sanjayaherath/Child-Watch/sketches/time_ds3231/time_ds3231.ino

// Date and time functions using a DS3231 RTC connected via I2C and Wire lib
#include <Wire.h>
#include "RTClib.h"

RTC_DS3231 rtc;

//char daysOfTheWeek[7][12] = {"Sunday", "Monday", "Tuesday", "Wednesday", "Thursday", "Friday", "Saturday"};

void setup () {


  Serial.begin(9600);

  delay(3000); // wait for console opening

  if (! rtc.begin()) {
    Serial.println("Couldn't find RTC");
    while (1);
  }

  if (rtc.lostPower()) {
    
    rtc.adjust(DateTime(F(__DATE__), F(__TIME__)));
    // This line sets the RTC with an explicit date & time, for example to set
    // January 1, 2000 at 12am you would call:
     rtc.adjust(DateTime(2000, 1, 1, 0, 0, 0));
  }
}

void loop () {
    DateTime now = rtc.now();
    
    Serial.print(now.year(), DEC);
    Serial.print('/');
    Serial.print(now.month(), DEC);
    Serial.print('/');
    Serial.print(now.day(), DEC);
    Serial.print(" ");
    //Serial.print(daysOfTheWeek[now.dayOfTheWeek()]);
    //Serial.print(") ");
    Serial.print(now.hour(), DEC);
    Serial.print(':');
    Serial.print(now.minute(), DEC);
    Serial.print(':');
    Serial.print(now.second(), DEC);
    Serial.println();
    
    
    
    
    delay(3000);
}
