sanjayaherath/Child-Watch/sketches/FONAtest2/FONAtest2.ino

#include "Adafruit_FONA.h"

#define FONA_RX 2
#define FONA_TX 3
#define FONA_RST 4


char replybuffer[255];


#include <SoftwareSerial.h>
SoftwareSerial fonaSS = SoftwareSerial(FONA_TX, FONA_RX);
SoftwareSerial *fonaSerial = &fonaSS;


Adafruit_FONA fona = Adafruit_FONA(FONA_RST);


uint8_t readline(char *buff, uint8_t maxbuff, uint16_t timeout = 0);

void setup() {
  while (!Serial);

  Serial.begin(115200);
  Serial.println(F("FONA basic test"));
  Serial.println(F("Initializing....(May take 3 seconds)"));

  fonaSerial->begin(4800);
  if (! fona.begin(*fonaSerial)) {
    Serial.println(F("Couldn't find FONA"));
    while (1);
  }
 
  Serial.println(F("FONA is OK"));
  Serial.print(F("Found "));
 
  printMenu();
}

void printMenu(void) {
  
  Serial.println(F("[?] Print this menu"));
  
  // Phone
  Serial.println(F("[c] make phone Call"));
  Serial.println(F("[A] get call status"));
  Serial.println(F("[h] Hang up phone"));
  Serial.println(F("[p] Pick up phone"));

  // SMS
  Serial.println(F("[N] Number of SMSs"));
  Serial.println(F("[r] Read SMS #"));
  Serial.println(F("[R] Read All SMS"));
  Serial.println(F("[d] Delete SMS #"));
  Serial.println(F("[s] Send SMS"));
  Serial.println(F("[u] Send USSD"));
  
  // Time
  Serial.println(F("[y] Enable network time sync (FONA 800 & 808)"));
  Serial.println(F("[Y] Enable NTP time sync (GPRS FONA 800 & 808)"));
  Serial.println(F("[t] Get network time"));


}
void loop() {
  Serial.print(F("FONA> "));
  while (! Serial.available() ) {
    if (fona.available()) {
      Serial.write(fona.read());
    }
  }

  char command = Serial.read();
  Serial.println(command);


  switch (command) {
    case '?': {
        printMenu();
        break;
      }



  

    /*** Call ***/
    case 'c': {
        // call a phone!
        char number[30];
        flushSerial();
        Serial.print(F("Call #"));
        readline(number, 30);
        Serial.println();
        Serial.print(F("Calling ")); Serial.println(number);
        if (!fona.callPhone(number)) {
          Serial.println(F("Failed"));
        } else {
          Serial.println(F("Sent!"));
        }

        break;
      }
    case 'A': {
        // get call status
        int8_t callstat = fona.getCallStatus();
        switch (callstat) {
          case 0: Serial.println(F("Ready")); break;
          case 1: Serial.println(F("Could not get status")); break;
          case 3: Serial.println(F("Ringing (incoming)")); break;
          case 4: Serial.println(F("Ringing/in progress (outgoing)")); break;
          default: Serial.println(F("Unknown")); break;
        }
        break;
      }
      
    case 'h': {
        // hang up!
        if (! fona.hangUp()) {
          Serial.println(F("Failed"));
        } else {
          Serial.println(F("OK!"));
        }
        break;
      }

    case 'p': {
        // pick up!
        if (! fona.pickUp()) {
          Serial.println(F("Failed"));
        } else {
          Serial.println(F("OK!"));
        }
        break;
      }

    /*** SMS ***/

    case 'N': {
        // read the number of SMS's!
        int8_t smsnum = fona.getNumSMS();
        if (smsnum < 0) {
          Serial.println(F("Could not read # SMS"));
        } else {
          Serial.print(smsnum);
          Serial.println(F(" SMS's on SIM card!"));
        }
        break;
      }
    case 'r': {
        // read an SMS
        flushSerial();
        Serial.print(F("Read #"));
        uint8_t smsn = readnumber();
        Serial.print(F("\n\rReading SMS #")); Serial.println(smsn);

        // Retrieve SMS sender address/phone number.
        if (! fona.getSMSSender(smsn, replybuffer, 250)) {
          Serial.println("Failed!");
          break;
        }
        Serial.print(F("FROM: ")); Serial.println(replybuffer);

        // Retrieve SMS value.
        uint16_t smslen;
        if (! fona.readSMS(smsn, replybuffer, 250, &smslen)) { // pass in buffer and max len!
          Serial.println("Failed!");
          break;
        }
        Serial.print(F("***** SMS #")); Serial.print(smsn);
        Serial.print(" ("); Serial.print(smslen); Serial.println(F(") bytes *****"));
        Serial.println(replybuffer);
        Serial.println(F("*****"));

        break;
      }
    case 'R': {
        // read all SMS
        int8_t smsnum = fona.getNumSMS();
        uint16_t smslen;
        int8_t smsn;

        
        for ( ; smsn <= smsnum; smsn++) {
          Serial.print(F("\n\rReading SMS #")); Serial.println(smsn);
          if (!fona.readSMS(smsn, replybuffer, 250, &smslen)) {  // pass in buffer and max len!
            Serial.println(F("Failed!"));
            break;
          }
          // if the length is zero, its a special case where the index number is higher
          // so increase the max we'll look at!
          if (smslen == 0) {
            Serial.println(F("[empty slot]"));
            smsnum++;
            continue;
          }

          Serial.print(F("***** SMS #")); Serial.print(smsn);
          Serial.print(" ("); Serial.print(smslen); Serial.println(F(") bytes *****"));
          Serial.println(replybuffer);
          Serial.println(F("*****"));
        }
        break;
      }

    case 'd': {
        // delete an SMS
        flushSerial();
        Serial.print(F("Delete #"));
        uint8_t smsn = readnumber();

        Serial.print(F("\n\rDeleting SMS #")); Serial.println(smsn);
        if (fona.deleteSMS(smsn)) {
          Serial.println(F("OK!"));
        } else {
          Serial.println(F("Couldn't delete"));
        }
        break;
      }

    case 's': {
        // send an SMS!
        char sendto[21], message[141];
        flushSerial();
        Serial.print(F("Send to #"));
        readline(sendto, 20);
        Serial.println(sendto);
        Serial.print(F("Type out one-line message (140 char): "));
        readline(message, 140);
        Serial.println(message);
        if (!fona.sendSMS(sendto, message)) {
          Serial.println(F("Failed"));
        } else {
          Serial.println(F("Sent!"));
        }

        break;
      }

    case 'u': {
      // send a USSD!
      char message[141];
      //flushSerial();
      Serial.print(F("Type out one-line message (140 char): "));
      readline(message, 140);
      Serial.println(message);

      uint16_t ussdlen;
      if (!fona.sendUSSD(message, replybuffer, 250, &ussdlen)) { // pass in buffer and max len!
        Serial.println(F("Failed"));
      } else {
        Serial.println(F("Sent!"));
        Serial.print(F("***** USSD Reply"));
        Serial.print(" ("); Serial.print(ussdlen); Serial.println(F(") bytes *****"));
        Serial.println(replybuffer);
        Serial.println(F("*****"));
      }
    }

    /*** Time ***/

    case 'y': {
        // enable network time sync
        if (!fona.enableNetworkTimeSync(true))
          Serial.println(F("Failed to enable"));
        break;
      }

    case 'Y': {
        // enable NTP time sync
        if (!fona.enableNTPTimeSync(true, F("pool.ntp.org")))
          Serial.println(F("Failed to enable"));
        break;
      }

    case 't': {
        // read the time
        char buffer[23];

        fona.getTime(buffer, 23);  // make sure replybuffer is at least 23 bytes!
        Serial.print(F("Time = ")); Serial.println(buffer);
        break;
      }

    default: {
        Serial.println(F("Unknown command"));
        printMenu();
        break;
      }
       // flush input
  flushSerial();
  while (fona.available()) {
    Serial.write(fona.read());
  }
 

}

}

void flushSerial() {
  while (Serial.available())
    Serial.read();
}

char readBlocking() {
  while (!Serial.available());
  return Serial.read();
}
uint16_t readnumber() {
  uint16_t x = 0;
  char c;
  while (! isdigit(c = readBlocking())) {
    //Serial.print(c);
  }
  Serial.print(c);
  x = c - '0';
  while (isdigit(c = readBlocking())) {
    Serial.print(c);
    x *= 10;
    x += c - '0';
  }
  return x;
}

uint8_t readline(char *buff, uint8_t maxbuff, uint16_t timeout) {
  uint16_t buffidx = 0;
  boolean timeoutvalid = true;
  if (timeout == 0) timeoutvalid = false;

  while (true) {
    if (buffidx > maxbuff) {
      //Serial.println(F("SPACE"));
      break;
    }

    while (Serial.available()) {
      char c =  Serial.read();

      //Serial.print(c, HEX); Serial.print("#"); Serial.println(c);

      if (c == '\r') continue;
      if (c == 0xA) {
        if (buffidx == 0)   // the first 0x0A is ignored
          continue;

        timeout = 0;         // the second 0x0A is the end of the line
        timeoutvalid = true;
        break;
      }
      buff[buffidx] = c;
      buffidx++;
    }

    if (timeoutvalid && timeout == 0) {
      //Serial.println(F("TIMEOUT"));
      break;
    }
    delay(1);
  }
  buff[buffidx] = 0;  // null term
  return buffidx;
}
